eric-handley/a3-srad-cameras/docs/arducam/Arducam IMX519 B0371.pdf

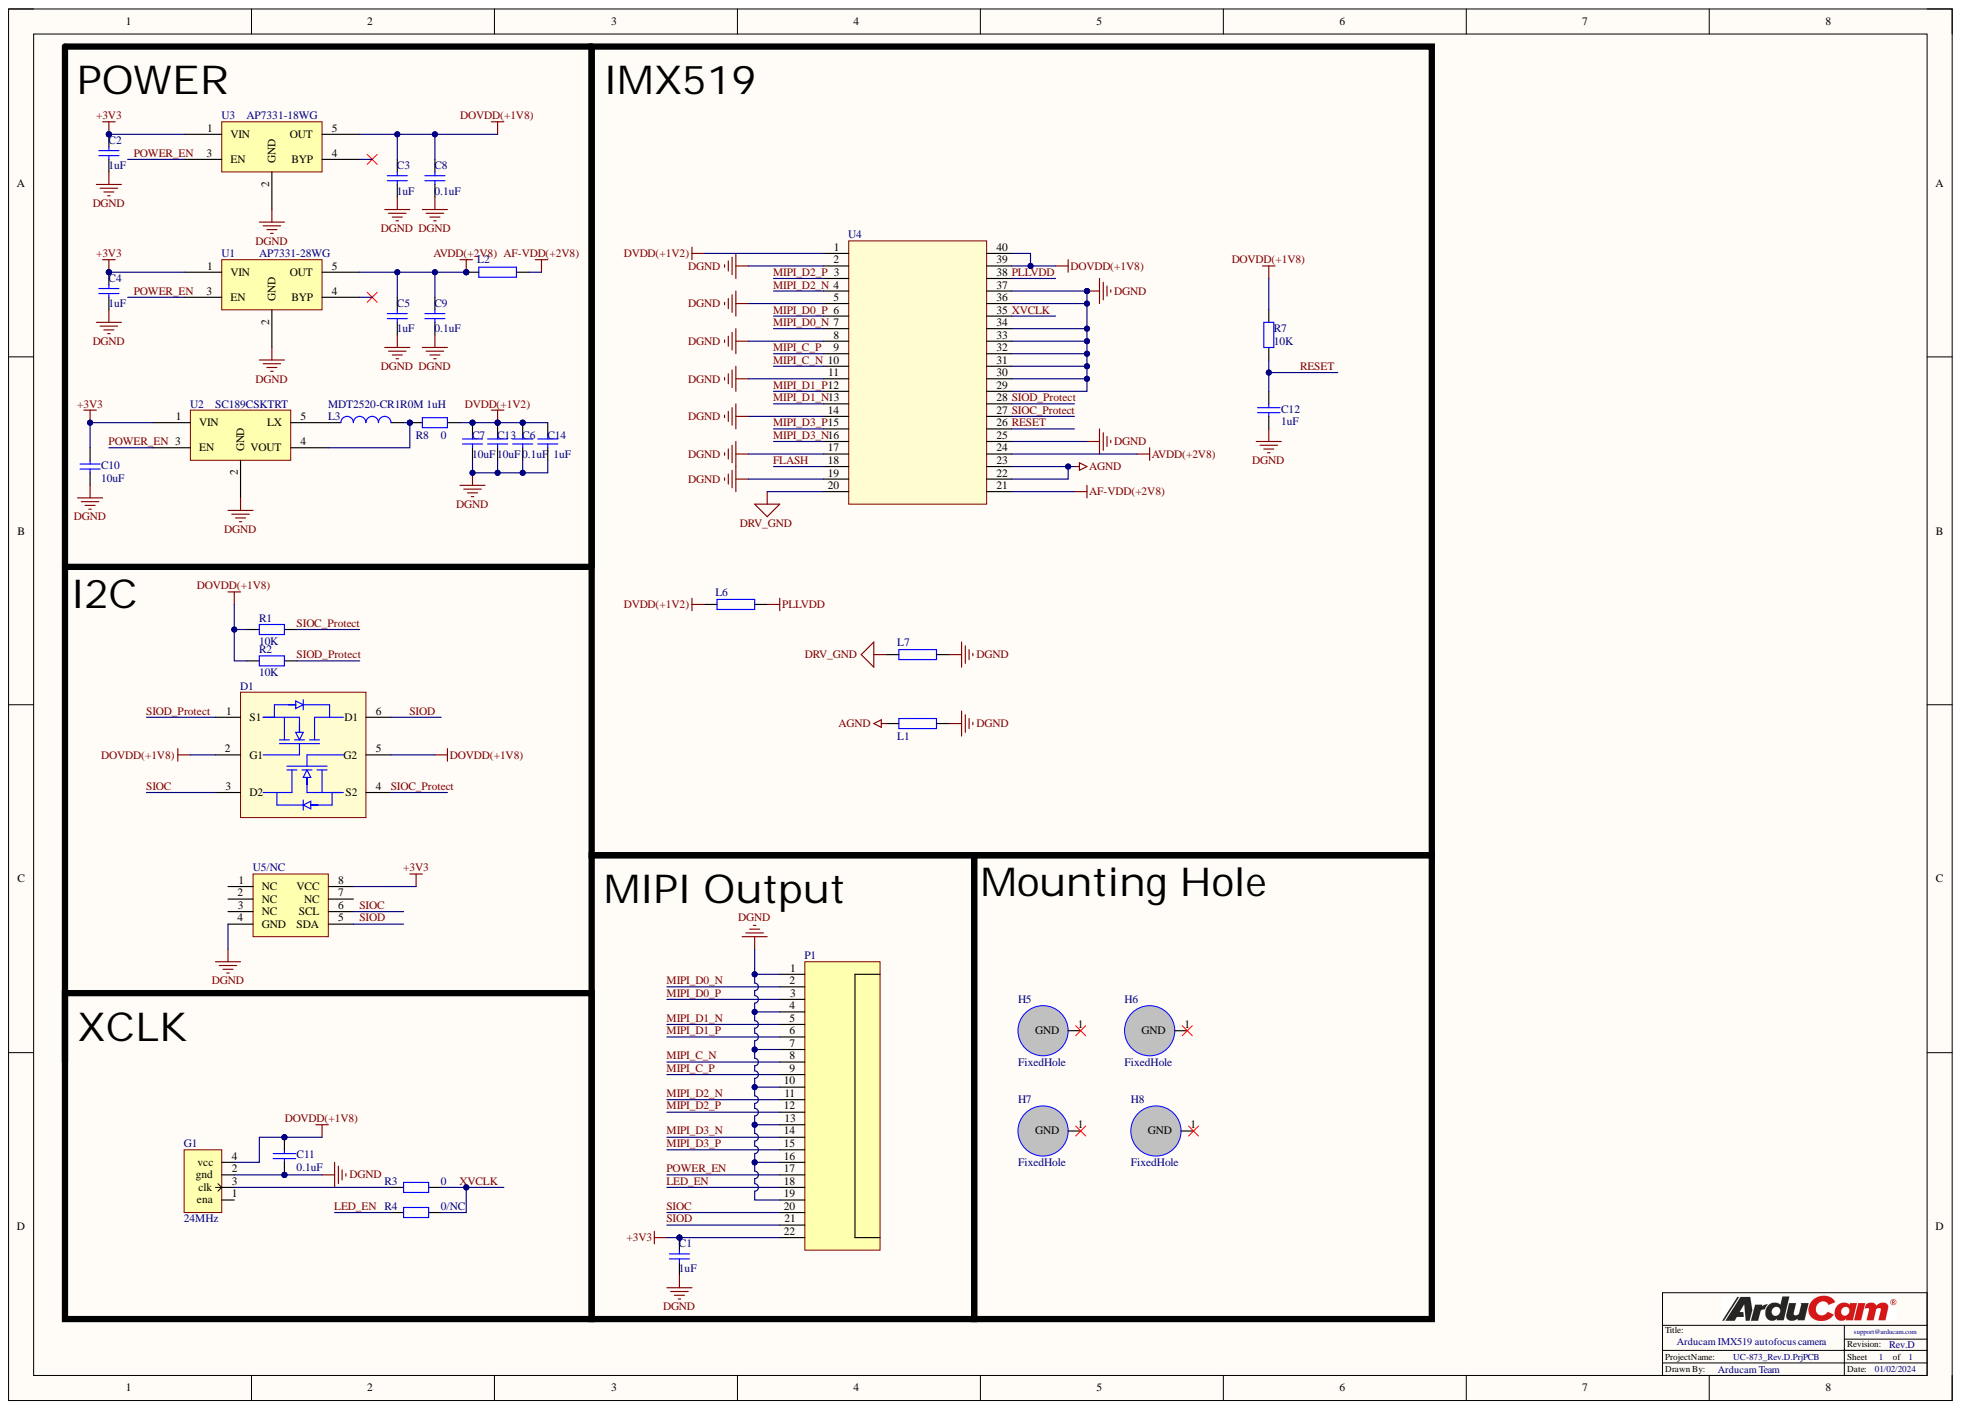
[picture p18: page 1]

ProjectName: UC-873_Rev.D.PrjPCB | Sheet 1 of 1
Drawn By: Arducam Team | Date: 01/02/2024
