eric-handley/a3-srad-cameras/stm32/Usr/Inc/thread_manager.h

#pragma once

#include "common.h"

#include "threads/imu_reader_thread.h"
#include "threads/controller_thread.h"
#include "threads/status_led_thread.h"

#define THREAD_STACK_SIZE 1024

#define IMU_PRIORITY        1
#define CONTROLLER_PRIORITY 0
#define STATUS_LED_PRIORITY 2

/*
    @brief Initializes user defined threads
    @returns - `TX_FALSE` if any thread fails to start. Successful threads are deleted
    @returns - `TX_TRUE` if all threads are initialized successfully
*/
bool init_threads();
